AkBKukU/CM153-Repro/img-ref/alt-angle.png

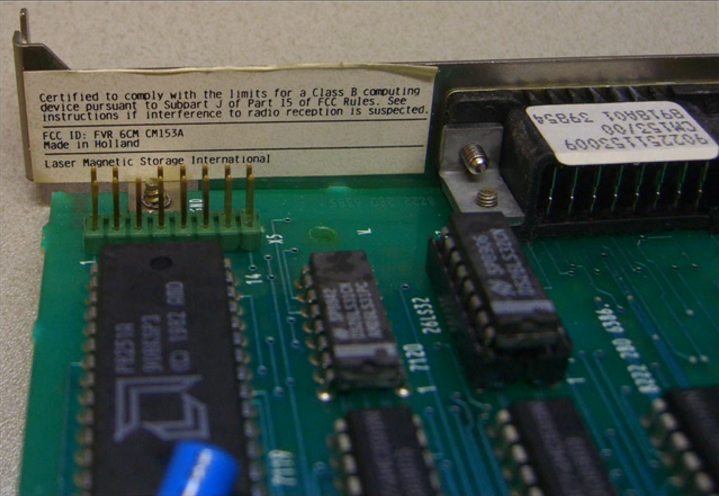
img-ref/alt-angle.png
