AkBKukU/CM153-Repro/img-ref/diff-rev/front-alt.jpeg

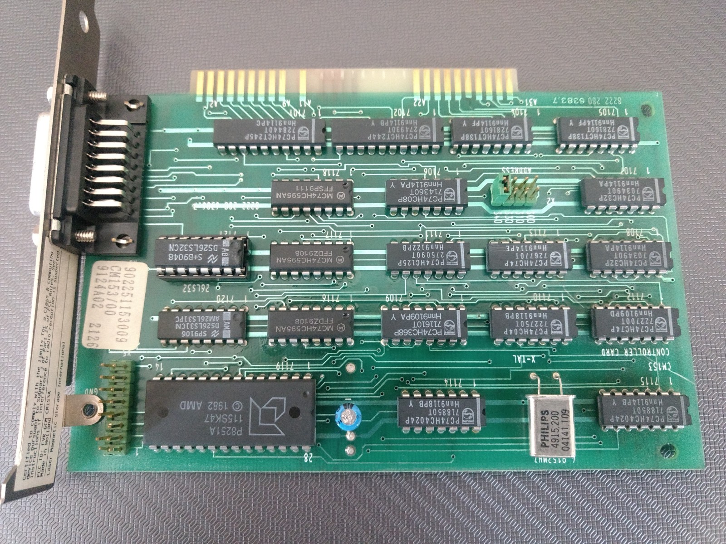
img-ref/diff-rev/front-alt.jpeg
