AkBKukU/CM153-Repro/img-ref/DSC06141.JPG

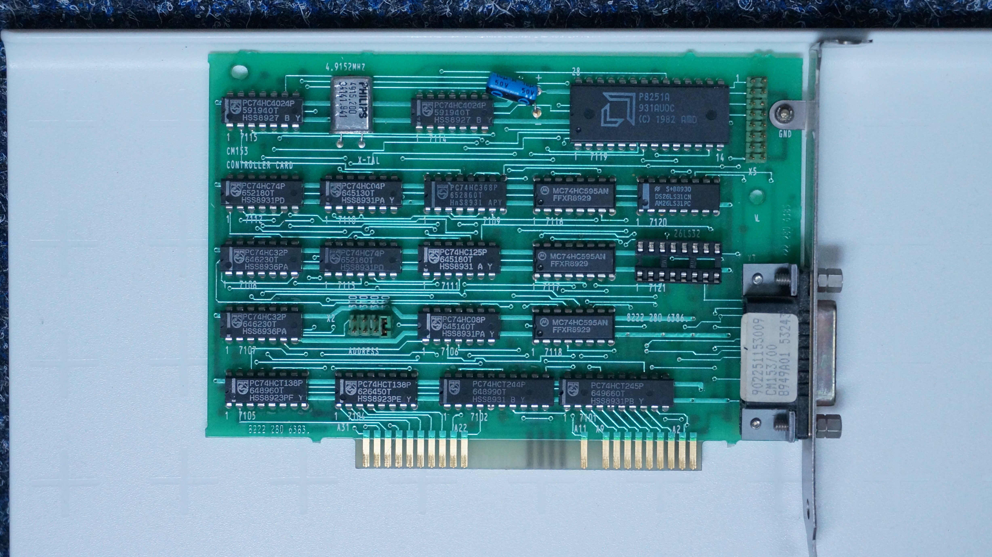
img-ref/DSC06141.JPG
