AkBKukU/CM153-Repro/img-ref/DSC06143.JPG

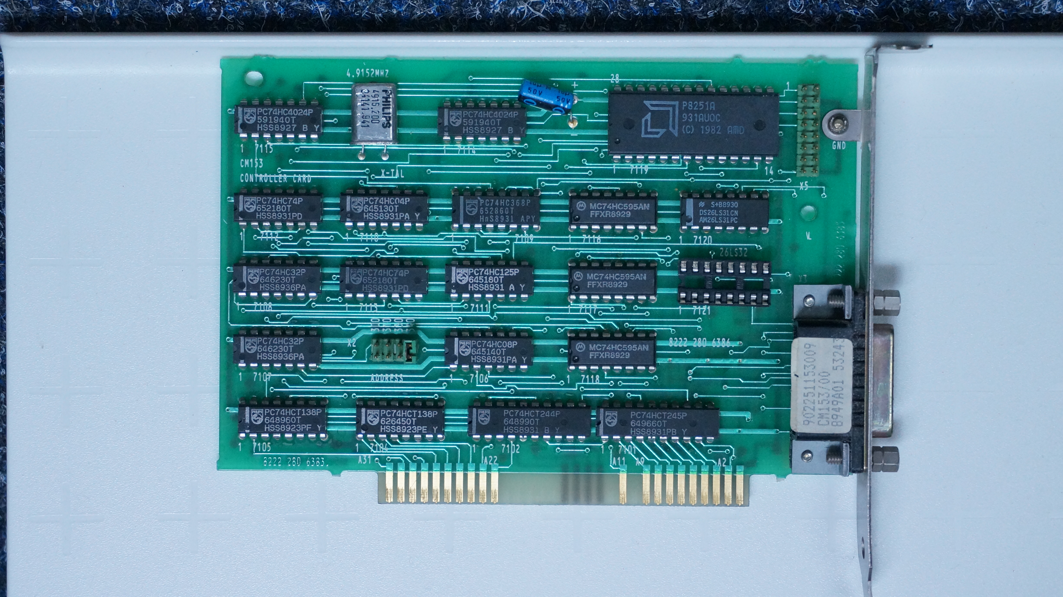
img-ref/DSC06143.JPG
