AkBKukU/CM153-Repro/img-ref/Scan 01084.jpg

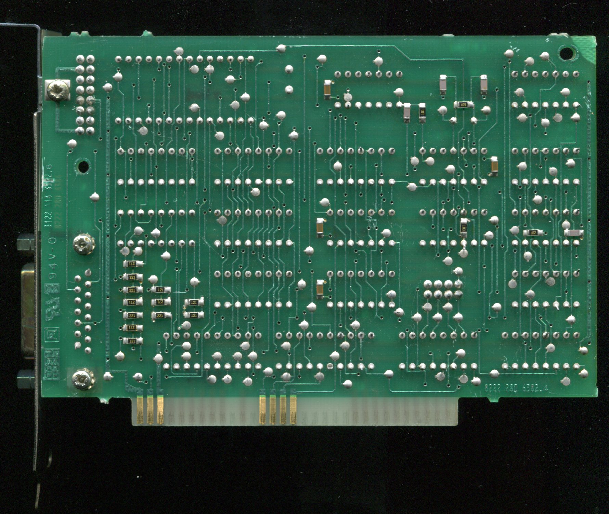
img-ref/Scan 01084.jpg
